nathanpc/Mini6/images/Amplifier (Rev A).png

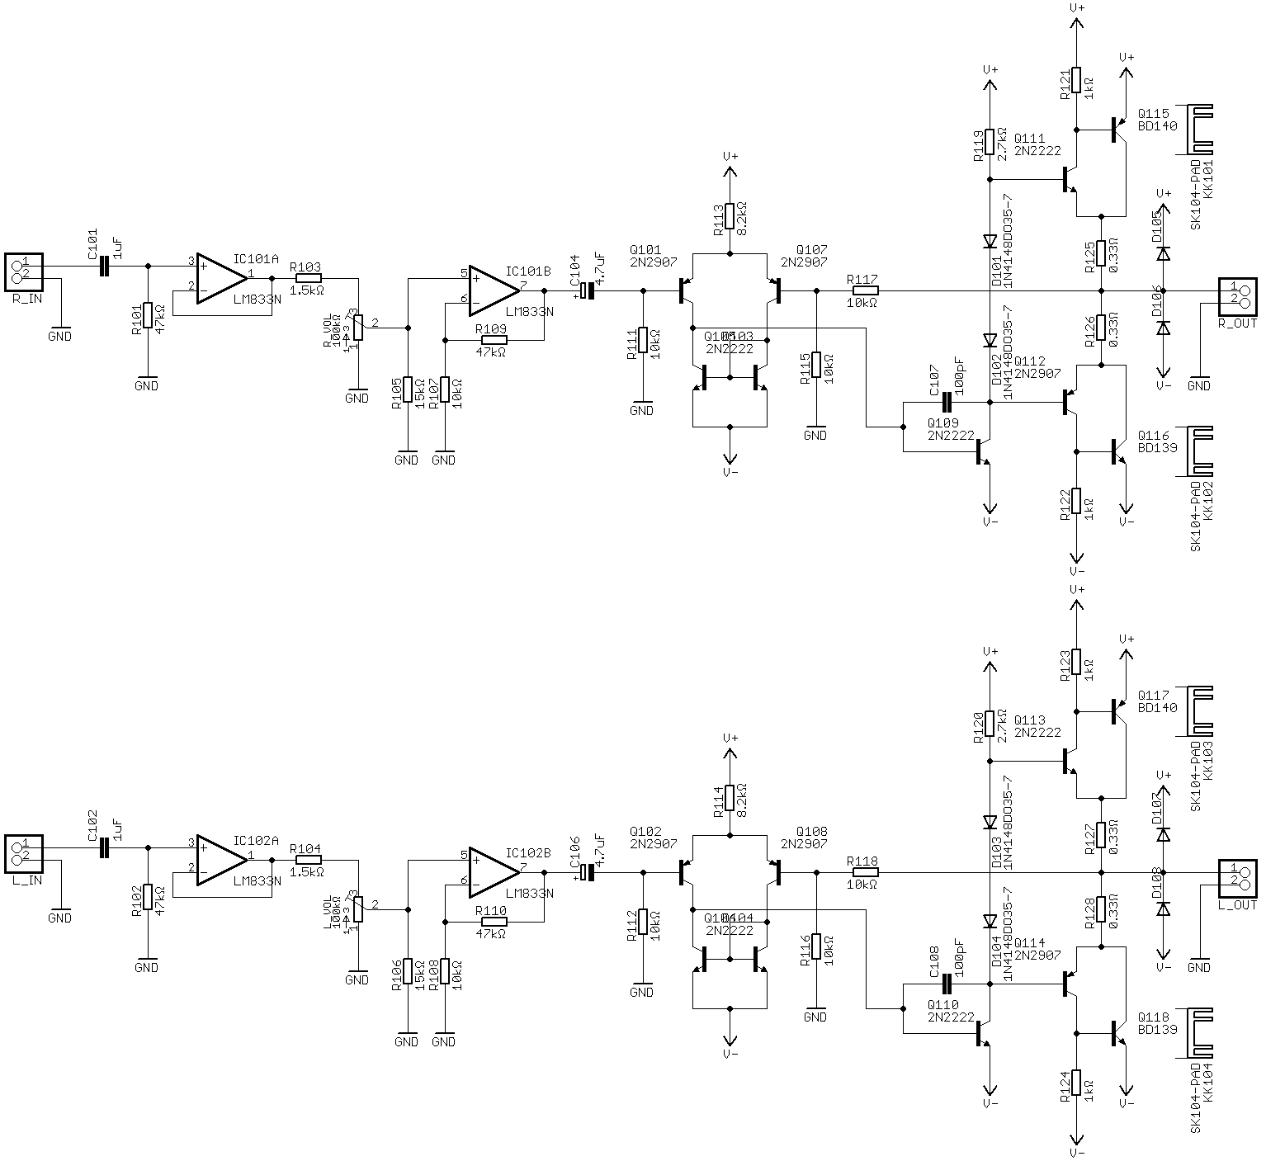
images/Amplifier (Rev A).png
